saegersven/robocup24/tests/test.png

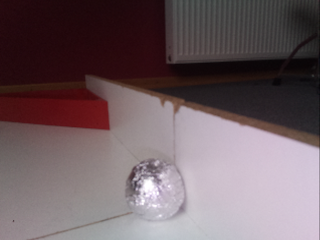
tests/test.png
