saegersven/robocup24/tests/tflite_c_api_test/test_images/1.png

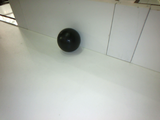
tests/tflite_c_api_test/test_images/1.png
