saegersven/robocup24/tests/tflite_c_api_test/test_images/3.png

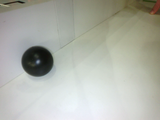
tests/tflite_c_api_test/test_images/3.png
