saegersven/robocup24/src/motions.h

/**************************************************************************************************************
 *                                                                                                            *
 * MOTIONS                                                                                                    *
 *                                                                                                            *
 * Contains specific movement sequences the robot does (e.g. picking up victims).                             *
 * This is all in a separate file to avoid cluttering the main program.                                       *
 *                                                                                                            *
 **************************************************************************************************************/

#pragma once

void pick_up_victim();
