saegersven/robocup24/src/rescue/rescue.c

#include "rescue.h"

#include <stdio.h>
#include <math.h>
#include <string.h>
#include <stdbool.h>

#include "../vision.h"
#include "../camera.h"
#include "../thresholding.h"
#include "../utils.h"
#include "../robot.h"

#include "victims.h"
#include "corner.h"
#include "silver.h"

// TuhDu (@Sven):
// cooldown when exit front detect
// test front exit

static DECLARE_S_IMAGE(frame, RESCUE_FRAME_WIDTH, RESCUE_FRAME_HEIGHT, 3);

// accurate flag uses rescue_reposition for improved accuracy
void rescue_find_center(bool accurate) {
	robot_serial_reset();
	const int MAX_TIME = 2500;

	for(int i = 0; i < 2; i++) {
		long long start_time = milliseconds();

		while(milliseconds() - start_time < MAX_TIME) {
			int dist = robot_sensor(DIST_FRONT);
			delay(30);
			if(dist > 800 && dist < 1100) {
				if(i == 1) {
					robot_drive(127, 35, 0);
				} else {
					robot_drive(35, 127, 0);
				}
			} else if (dist < 500) {
				if(i == 1) {
					robot_drive(-35, -127, 0);
				} else {
					robot_drive(-127, -35, 0);
				}
			} else {
				if(i == 1) {
					robot_drive(60, -60, 0);
				} else {
					robot_drive(-60, 60, 0);
				}
			}
		}
	}
	robot_drive(-80, -80, 300);
	robot_stop();

	if (accurate) rescue_reposition();
}

void rescue_reposition() {
	int dist_front = robot_distance_avg(DIST_FRONT, 10, 3);
	int dist_right_front = robot_distance_avg(DIST_RIGHT_FRONT, 10, 3);
	int dist_right_rear = robot_distance_avg(DIST_RIGHT_REAR, 10, 3);

	// exit somewhere, turn a bit and try again
	if ((dist_front > 1000) | (dist_right_front > 1000) | (dist_right_rear > 1000)) {
		robot_drive(100, -100, 73);
		rescue_reposition();
		return;
	}

	float x = (dist_right_front + dist_right_rear) / 2.0f - 500;
	float y = dist_front - 500;

	float angle = atan2f(x, y);
	float mag = sqrtf(x*x + y*y);

	robot_turn(angle);
	robot_drive(100, 100, mag * 2);
}

void rescue_collect_victim() {
	// DO THE COLLECTING THING
	robot_servo(SERVO_STRING, STRING_POS_OPEN, false, false);
    robot_servo(SERVO_ARM, ARM_POS_HALF_DOWN, false, false);
    delay(800);
    printf("Driving forward\n");
    robot_drive(70, 70, 0);
    delay(200);
    robot_servo(SERVO_ARM, ARM_POS_DOWN, true, true);
    delay(100);
    robot_stop();
    delay(300);
    robot_servo(SERVO_ARM, ARM_POS_DOWN, true, true);
    robot_drive(-70, -70, 200);
    robot_drive(70, 70, 200);
    delay(200);
    robot_servo(SERVO_STRING, STRING_POS_CLOSED, false, false);
    delay(450);
    robot_drive(-70, -70, 600);
    robot_servo(SERVO_ARM, ARM_POS_UP, false, false);
    delay(400);
}

// Returns 0 if no victim was found, 1 if victim is alive and 2 if victim is dead
int rescue_collect(int find_dead) {
	display_set_number(NUMBER_RESCUE_OBJECTIVE, RESCUE_OBJECTIVE_VICTIM);

	struct Victim victim;

	int cam_angle = CAM_POS_UP;
	robot_servo(SERVO_CAM, cam_angle, false, false);

	int final_approach = 0;

	int turn_counter = 0;
	int none_found_counter = 0;

	float classification_accumulator = 0.0f;
	int num_classifications = 0;
	//camera_start_capture(RESCUE_CAPTURE_WIDTH, RESCUE_CAPTURE_HEIGHT);
	while(1) {
		robot_stop();
		delay(60);
		camera_start_capture(RESCUE_CAPTURE_WIDTH, RESCUE_CAPTURE_HEIGHT);
		camera_grab_frame(frame, RESCUE_FRAME_WIDTH, RESCUE_FRAME_HEIGHT);
		camera_stop_capture();
		printf("Frame grabbed\n");
		int ret = victims_find(frame, find_dead, &victim);
		printf("%d\n", ret);
		delay(10);

		if(ret) {
			num_classifications++;
			classification_accumulator += victim.dead;
			display_set_number(NUMBER_RESCUE_POS_X, victim.x);
			display_set_number(NUMBER_RESCUE_POS_Y, victim.y);
			display_set_number(NUMBER_RESCUE_IS_DEAD, victim.dead + 1);

			float angle_horizontal = (victim.x - 0.5f) * CAM_HORIZONTAL_FOV;
			robot_turn(angle_horizontal);

			printf("Victim at (%f, %f)\n", victim.x, victim.y);

			if(final_approach) {
				int duration = (0.5f - victim.y) * 500;
				robot_drive(50, 50, duration);

				if(victim.x > 0.45f && victim.x < 0.55f
					&& victim.y > 0.42f && victim.y < 0.58f) {
					robot_turn(DTOR(30.0f));
					delay(50);
					robot_drive(-60, -60, 180);
					delay(50);
					rescue_collect_victim();
					//camera_stop_capture();
					return (int)roundf(classification_accumulator / num_classifications) + 1;
				}
			} else {
				float angle_vertical = (victim.y - 0.5f) * CAM_VERTICAL_FOV;
				printf("Angle vertical: %f\n", RTOD(angle_vertical));

				float alpha = DTOR(cam_angle - CAM_POS_HORIZONTAL) + angle_vertical;
				if(alpha < 0.1f) alpha = 0.1f;
				float dist = CAM_HEIGHT_MM / alpha;
				int duration = dist * 0.6f;
				printf("Duration: %d\n", duration);
				robot_drive(80, 80, duration);


				float beta = atanf(CAM_HEIGHT_MM / dist);
				if(dist < 400.0f) beta = 0.0f;
				printf("Beta: %f\n", beta);
				cam_angle += RTOD(angle_vertical + beta);

				printf("New cam angle: %d\n", cam_angle);

				robot_servo(SERVO_CAM, cam_angle, false, false);

				if(cam_angle > 110 && dist < 105.0f) {
					printf("Final approach\n");
					cam_angle = 120;
					robot_servo(SERVO_CAM, cam_angle, false, false);
					final_approach = 1;
				}
			}
		} else {
			display_set_number(NUMBER_RESCUE_POS_X, 0.0f);
			display_set_number(NUMBER_RESCUE_POS_Y, 0.0f);
			display_set_number(NUMBER_RESCUE_IS_DEAD, 0.0f);

			num_classifications = 0;
			classification_accumulator = 0.0f;

			cam_angle = CAM_POS_UP;
			robot_servo(SERVO_CAM, cam_angle, false, false);
			final_approach = 0;

			robot_turn(DTOR(30.0f));
			turn_counter++;
			delay(250);
			if(turn_counter == 12) {
				if(none_found_counter == 1) {
					find_dead = 1;
				}
				rescue_find_center(0);
				none_found_counter++;
				turn_counter = 0;
			}
		}
	}
}

int rescue_collect_test(int find_dead) {
	display_set_number(NUMBER_RESCUE_OBJECTIVE, RESCUE_OBJECTIVE_VICTIM);

	struct Victim victim;

	int cam_angle = CAM_POS_UP;
	robot_servo(SERVO_CAM, cam_angle, false, false);

	camera_start_capture(RESCUE_CAPTURE_WIDTH, RESCUE_CAPTURE_HEIGHT);

	while(1) {
		camera_grab_frame(frame, RESCUE_FRAME_WIDTH, RESCUE_FRAME_HEIGHT);

		int ret = victims_find(frame, find_dead, &victim);
		
		if(ret) {
			display_set_number(NUMBER_RESCUE_POS_X, victim.x);
			display_set_number(NUMBER_RESCUE_POS_Y, victim.y);
			display_set_number(NUMBER_RESCUE_IS_DEAD, victim.dead + 1);

			float angle_horizontal = (victim.x - 0.5f) * CAM_HORIZONTAL_FOV;
			
			float u = 20 * angle_horizontal;
			robot_drive(30 + u, 30 - u, 0);

			float angle_vertical = (victim.y - 0.5f) * CAM_VERTICAL_FOV;
			float v = 10 * angle_vertical;
			cam_angle += v;
			robot_servo(SERVO_CAM, cam_angle, false, false);
		} else {
			display_set_number(NUMBER_RESCUE_POS_X, 0.0f);
			display_set_number(NUMBER_RESCUE_POS_Y, 0.0f);
			display_set_number(NUMBER_RESCUE_IS_DEAD, 0.0f);

			cam_angle = CAM_POS_UP;
			robot_servo(SERVO_CAM, cam_angle, false, false);

			robot_turn(DTOR(30.0f));
			delay(250);
		}
	}
}

void rescue_drop_victim() {
	delay(200);
    robot_servo(SERVO_STRING, STRING_POS_OPEN, true, true);
    delay(500);
    robot_servo(SERVO_STRING, STRING_POS_OPEN, false, false);
    robot_servo(SERVO_ARM, ARM_POS_HALF_DOWN, true, true);
    delay(1000);
    robot_servo(SERVO_STRING, STRING_POS_CLOSED, true, true);
    delay(400);
    robot_servo(SERVO_STRING, STRING_POS_OPEN, false, false);
    delay(400);
    robot_servo(SERVO_ARM, ARM_POS_UP, true, true);
    delay(250);
    robot_servo(SERVO_ARM, ARM_POS_HALF_DOWN, true, true);
    delay(250);
    robot_servo(SERVO_ARM, ARM_POS_UP, true, true);
    delay(250);
    robot_servo(SERVO_ARM, ARM_POS_HALF_DOWN, true, true);
    delay(250);
    robot_servo(SERVO_ARM, ARM_POS_UP, false, false);
    delay(600);
}

void rescue_deliver(int is_dead) {
	display_set_number(NUMBER_RESCUE_OBJECTIVE, RESCUE_OBJECTIVE_CORNER);

	robot_servo(SERVO_CAM, CAM_POS_UP, false, false);
	
	delay(300);
	camera_start_capture(RESCUE_CAPTURE_WIDTH, RESCUE_CAPTURE_HEIGHT);
	for(int i = 0; i < 5; i++) camera_grab_frame(frame, RESCUE_FRAME_WIDTH, RESCUE_FRAME_HEIGHT);
	camera_stop_capture();
	delay(200);
	//camera_start_capture(RESCUE_CAPTURE_WIDTH, RESCUE_CAPTURE_HEIGHT);

	long long start_time = milliseconds();

	int turn_counter = 0;
	while(1) {
		robot_turn(DTOR(20.0f));
		delay(250);

		camera_start_capture(RESCUE_CAPTURE_WIDTH, RESCUE_CAPTURE_HEIGHT);
		camera_grab_frame(frame, RESCUE_FRAME_WIDTH, RESCUE_FRAME_HEIGHT);
		camera_stop_capture();

		delay(50);

		float x = 0.0f;
		if(corner_detect(frame, &x, !is_dead, milliseconds() - start_time)) {
			printf("Corner pos: %f\n", x);

			robot_stop();
			delay(50);

			robot_turn(x * DTOR(65.0f) + DTOR(1.0f));

			int alignment_successful = 1;
			// Align for final approach
			for(int i = 0; i < 8; i++) {
				camera_start_capture(RESCUE_CAPTURE_WIDTH, RESCUE_CAPTURE_HEIGHT);
				camera_grab_frame(frame, RESCUE_FRAME_WIDTH, RESCUE_FRAME_HEIGHT);
				camera_stop_capture();
				delay(50);

				if(!corner_detect(frame, &x, !is_dead, milliseconds() - start_time)) {
					if(i < 3) {
						printf("Lost corner");
						robot_turn(-DTOR(20.0f));
						alignment_successful = 0;
					}
					x = 0.0f;
					break;
				}

				robot_turn(x * DTOR(65.0f) + DTOR(1.0f));
				if(i > 1) robot_drive(45, 45, 700);
				delay(80);
			}

			if(!alignment_successful) continue;

			// Robot is aligned with corner, approach

			/*
			robot_drive(40, 40, 1600);
			robot_drive(-80, -80, 200);
			robot_turn(DTOR(25.0f));
			robot_drive(40, 40, 650);
			*/
			robot_drive(-100, 0, 250);
			robot_drive(0, -100, 350);
			robot_drive(40, 40, 1150);

			// Drop victim
			rescue_drop_victim();

			// Go back to center
			if (!is_dead) {
				robot_drive(-100, -100, 600);
				robot_turn(DTOR(45.0f)); // face away from corner to avoid detecting rescued victims (just to be safe)
			}

			//camera_stop_capture();
			return;
		}

		turn_counter++;

		if(turn_counter == 18) {
			rescue_find_center(0);

			turn_counter = 0;
		}
	}
}

const int CAPTURE_WIDTH = 320;
const int CAPTURE_HEIGHT = 192;
const int FRAME_WIDTH = 80;
const int FRAME_HEIGHT = 48;

// Counts red/green pixels
bool rescue_is_corner() {
	robot_servo(SERVO_CAM, 0.4 * (CAM_POS_UP + CAM_POS_DOWN), true, false);
	delay(300);

	const int NUM_PIXELS_THRESHOLD = 360;

	camera_grab_frame(frame, FRAME_WIDTH, FRAME_HEIGHT);

	int green_pixels = image_count_pixels(frame, FRAME_WIDTH, FRAME_HEIGHT, 3, is_green);
	int red_pixels = image_count_pixels(frame, FRAME_WIDTH, FRAME_HEIGHT, 3, is_red);

	printf("Num green pixels: %d \t Red pixels: %d \n", green_pixels, red_pixels);

	return green_pixels > NUM_PIXELS_THRESHOLD || red_pixels > NUM_PIXELS_THRESHOLD;
}

int is_black_exit(uint8_t b, uint8_t g, uint8_t r) {
	return (uint16_t)b + (uint16_t)g + (uint16_t)r < 120;
}

int is_gray(uint8_t b, uint8_t g, uint8_t r) {
	return (uint16_t)b + (uint16_t)g + (uint16_t)r < 250;
}

// Lets hope num black pixels is enough
bool rescue_is_exit() {
	//return true;
	const int NUM_PIXELS_THRESHOLD = 340;
	
	int max_num_pixels = 0;

	robot_drive(60, 60, 0);
	long long start_time = milliseconds();

	int sum_black_pixels = 0;
	const int N = 5;

	for(int i = 0; i < N; i++) {
		camera_grab_frame(frame, FRAME_WIDTH, FRAME_HEIGHT);

		int num_black_pixels = image_count_pixels_roi(frame, FRAME_WIDTH, FRAME_HEIGHT, 3, is_black_exit, 20, 60, 5, 43);
		sum_black_pixels += num_black_pixels;
		printf("Num black pixels: %d\n", num_black_pixels);

		if(num_black_pixels > max_num_pixels) max_num_pixels = num_black_pixels;

		robot_drive(60, 60, 80);
	}

	int avg_black_pixels = sum_black_pixels / N;

	printf("avg_black_pixels: %d\n", avg_black_pixels);
	printf("max_num_pixels: %d\n", max_num_pixels);

	return max_num_pixels > NUM_PIXELS_THRESHOLD;
}

// returns number of black pixels in current frame
int pixels_black() {
	robot_servo(SERVO_CAM, CAM_POS_DOWN - 10, true, false);
	delay(300);

	camera_start_capture(RESCUE_CAPTURE_WIDTH, RESCUE_CAPTURE_HEIGHT);
	camera_grab_frame(frame, RESCUE_FRAME_WIDTH, RESCUE_FRAME_HEIGHT);
	camera_stop_capture();
	printf("Black pixels: %d \n", image_count_pixels(frame, RESCUE_FRAME_WIDTH, RESCUE_FRAME_HEIGHT, 3, is_black));
    return image_count_pixels(frame, RESCUE_FRAME_WIDTH, RESCUE_FRAME_HEIGHT, 3, is_black);
}

// navigates around corner
int rescue_navigate_corner() {
	if (robot_distance_avg(DIST_RIGHT_FRONT, 10, 0.2f) < 70) {
		robot_drive(0, -100, 300);
		robot_drive(-100, 0, 400);
		robot_drive(40, 40, 1100);
	}
	robot_drive(-100, -100, 300);
	robot_turn(-R90);
	if (robot_distance_avg(DIST_FRONT, 10, 0.2f) > 1500) { //ohohoho exit in front
		
		camera_start_capture(RESCUE_CAPTURE_WIDTH, RESCUE_CAPTURE_HEIGHT);
		while(1) {
			robot_drive(60, 60, 0);
			camera_grab_frame(frame, RESCUE_FRAME_WIDTH, RESCUE_FRAME_HEIGHT);
			int num_pixels = image_count_pixels(frame, RESCUE_FRAME_WIDTH, RESCUE_FRAME_HEIGHT, 3, is_black);
			if(num_pixels > 200) break;
		}
		camera_stop_capture();

		robot_turn(DTOR(45.0f));
		robot_drive(100, 100, 300);

		return 1;
	} else {
		robot_drive(50, 50, 0);
		while (robot_sensor(DIST_FRONT) > 200);
		robot_stop();
		robot_turn(DTOR(135.0f));
		robot_drive(-100, -100, 250);
		robot_turn(-DTOR(175.0f));
		robot_drive(-100, -100, 250);
	}
	return 0;
}

void rescue_find_exit() {
	printf("I am in find exit now. Pls pray for me.\n");
	if(rescue_navigate_corner()) return;

	bool already_checked_for_corner = false;
	long long side_exit_cooldown = 0;

	long long last_time = milliseconds();
	int prev_error = 0;

	robot_servo(SERVO_CAM, CAM_POS_DOWN - 5, true, false);

	rescue_silver_init();

	camera_start_capture(CAPTURE_WIDTH, CAPTURE_HEIGHT);

	while(1) {
		int front_dist = robot_sensor(DIST_FRONT);
		int side_front_dist = robot_sensor(DIST_RIGHT_FRONT);
		int side_rear_dist = robot_sensor(DIST_RIGHT_REAR);

		// --- START OF WALLFOLLOWER LOGIC ---
		if(side_front_dist < 200 && side_rear_dist < 200) {
			const int SPEED = 50;
			const int TARGET_DIST_SIDE = 50;   // Target distance for the side sensor
			
			const float L = 113.0f;
			const float delta_D = 8.0f;

			const float KP = 0.4f;
			const float KD = 0.02f;
			const float KP_angle = 80.0f;

			float angle = atanf((float)(side_rear_dist + delta_D - side_front_dist) / L);

			// PD controller for side distance
			int side_dist_measurement = TARGET_DIST_SIDE - (side_front_dist + side_rear_dist + delta_D) / 2;
			float error = side_dist_measurement * cosf(angle);

			printf("Error: %.0f, Angle: %.2f\n", error, angle);

			long long time = milliseconds();
			float dt = (time - last_time) / 1000.0f;
			if(prev_error == 0) prev_error = error;
			float derivative = (error - prev_error) / dt;
			last_time = time;
			prev_error = error;

			int speed_adjustment = clamp(KP * error + KD * derivative + KP_angle * angle, -50, 50);

			int left_speed = SPEED - speed_adjustment;
			int right_speed = SPEED + speed_adjustment;

			// Only drive with calculates speeds when there is a wall
			robot_drive(left_speed, right_speed, 0);
		} else {
			robot_drive(50, 50, 0);
		}
		// --- END OF WALLFOLLOWER LOGIC ---

		// Check for exit with camera
		camera_grab_frame(frame, FRAME_WIDTH, FRAME_HEIGHT);

		int num_black_pixels = image_count_pixels(frame, FRAME_WIDTH, FRAME_HEIGHT, 3, is_gray);
		if(num_black_pixels > 400) {
			printf("Potential front exit\n");

			robot_stop();
			if(rescue_silver_detect_flipped(frame, 3) > 0.5f) {
				robot_drive(-60, -60, 150);
				if (!rescue_is_exit()) {
					// no exit, skip
					robot_drive(-80, -80, 500);
					robot_turn(DTOR(90.0f));
					robot_drive(-100, -100, 400);
					robot_turn(DTOR(-180.0f));
					robot_drive(-50, -50, 1200);
					side_exit_cooldown = milliseconds();
				} else return;
			}
		}

		// There are 4 different cases:

		// 1) 35cm in front of wall, check for corner
		// 2) 10cm in front of wall, turn 90°
		// 3) potential exit front
		// 4) potential exit side

		// 1. case
		if (!already_checked_for_corner &&
			front_dist < 360
			&& robot_stop()
			&& robot_distance_avg(DIST_FRONT, 5, 1) < 380) {

			printf("Case 1\n");
			if (rescue_is_corner()) {
				robot_drive(-100, -100, 200);
				delay(30);
				robot_turn(DTOR(132.0f));
				robot_drive(-100, -100, 300);
				robot_turn(-R90);
				robot_drive(40, 40, 1500);
				if(rescue_navigate_corner()) return;
			} else {
				already_checked_for_corner = true;
			}

			robot_servo(SERVO_CAM, CAM_POS_DOWN - 5, true, false);
		}

		// 2. case
		else if (front_dist < 130
			&& robot_stop()
			&& robot_distance_avg(DIST_FRONT, 5, 1) < 150) {

			printf("Case 2\n");
			robot_turn(DTOR(90.0f));
			robot_drive(-100, -100, 250);
			robot_turn(DTOR(-180.0f));
			robot_drive(-50, -50, 400);
			if (already_checked_for_corner) {
				robot_drive(-50, -50, 800);
			}
			already_checked_for_corner = false;
		}

		// 4. case
		if (milliseconds() - side_exit_cooldown > 3000 
			&& side_front_dist > 200 
			&& robot_stop() 
			&& robot_distance_avg(DIST_RIGHT_FRONT, 5, 1) > 180) {

			printf("Potential side exit\n");
			robot_drive(100, 100, 180);
			robot_turn(DTOR(90.0f));

			if (!rescue_is_exit()) {
				// no exit, skip
				robot_drive(-80, -80, 400);
				robot_turn(DTOR(-90.0f));
				side_exit_cooldown = milliseconds();
			} else {
				robot_drive(100, 100, 150);
				return;
			}
		}
	}
}
void rescue() {
	display_set_mode(MODE_RESCUE);
	display_set_image(IMAGE_RESCUE_FRAME, frame);
	display_set_image(IMAGE_RESCUE_THRESHOLD, corner_thresh);

	robot_serial_reset();

	robot_drive(100, 100, 800);

	int dist = robot_distance_avg(DIST_RIGHT_FRONT, 10, 2);
	printf("Dist right front: %d\n", dist);
	if(dist < 400) {
		robot_turn(DTOR(130.0f));
		robot_drive(-100, -100, 800);
		robot_turn(DTOR(85.0f));
	} else {
		robot_turn(DTOR(-130.0f));
		robot_drive(-100, -100, 800);
		robot_turn(DTOR(120.0f));
	}

	//camera_start_capture(RESCUE_CAPTURE_WIDTH, RESCUE_CAPTURE_HEIGHT);


	robot_servo(SERVO_CAM, CAM_POS_UP, false, false);
	robot_servo(SERVO_ARM, ARM_POS_UP, false, false);
	robot_servo(SERVO_STRING, STRING_POS_OPEN, false, false);

	victims_init();
	corner_init();

	display_set_number(NUMBER_RESCUE_OBJECTIVE, RESCUE_OBJECTIVE_VICTIM);

	int num_victims = 0;

	while(num_victims < 3) {
		display_set_number(NUMBER_RESCUE_NUM_VICTIMS, num_victims);

		int ret = rescue_collect(num_victims >= 2);

		if(ret) {
			rescue_deliver(ret == 2);
			if(ret == 2) {
				break;
			}
		} else {
			rescue_find_center(0);
			robot_drive(-70, -70, 400);
		}
		
		num_victims++;
	}
	robot_drive(35, 35, 1000);
	rescue_find_exit();

	rescue_cleanup();
}

void rescue_cleanup() {
	victims_destroy();
	corner_destroy();
	camera_stop_capture();
	delay(100);
}
