saegersven/robocup24/src/camera.c

#include "camera.h"

#include <string.h>
#include <stdio.h>
#include <stdint.h>
#include <errno.h>
#include <fcntl.h>
#include <sys/ioctl.h>
#include <sys/types.h>
#include <sys/time.h>
#include <sys/mman.h>
#include <linux/videodev2.h>
#include <pthread.h>
#include "../libs/libv4l/include/libv4l2.h"

#include "utils.h"

// Safe ioctl
static void xioctl(int fh, int request, void *arg) {
    int r;
    do {
        r = v4l2_ioctl(fh, request, arg);
    } while(r == -1 && ((errno = EINTR) || (errno == EAGAIN)));

    if(r == -1) {
	    fprintf(stderr, "error %d, %s\n", errno, strerror(errno));
	    exit(EXIT_FAILURE);
    }
}

static pthread_mutex_t frame_lock = PTHREAD_MUTEX_INITIALIZER;
static uint8_t *current_frame_ptr;
uint32_t current_width, current_height;
static uint32_t requested_width, requested_height;
static int has_frame;

static pthread_mutex_t signal_lock = PTHREAD_MUTEX_INITIALIZER;
static int stop_signal;

static pthread_t capture_thread_id;

static int camera_fd;

static const int NUM_BUFFERS = 2;

static int camera_running = 0;

void camera_start_capture(int width, int height) {
    stop_signal = 0;
    has_frame = 0;

    struct image_size *size = malloc(sizeof(struct image_size));
    size->width = width;
    size->height = height;
    requested_width = width;
    requested_height = height;
    
    pthread_create(&capture_thread_id, NULL, camera_capture_loop, (void*)size);
    pthread_detach(capture_thread_id);

    camera_running = 1;
}

void camera_stop_capture() {
    if(!camera_running) return;
    camera_running = 0;

    pthread_mutex_lock(&signal_lock);
    stop_signal = 1;
    pthread_mutex_unlock(&signal_lock);
}

void camera_grab_frame(uint8_t *frame, uint32_t width, uint32_t height) {
    pthread_mutex_lock(&frame_lock);

    // TODO: Add timeout
    while(!has_frame) {
        pthread_mutex_unlock(&frame_lock);
        usleep(100);
        pthread_mutex_lock(&frame_lock);
    }
    float factor_x = (float)requested_width / width;
    float factor_y = (float)requested_height / height;

    for(int i = 0; i < height; i++) {
        for(int j = 0; j < width; j++) {

            int dest_idx = i * width + j;
            int src_idx = factor_y * (height - 1 - i) * requested_width + factor_x * (width - 1 - j);

            for(int k = 0; k < 3; k++) {
                frame[3*dest_idx + k] = current_frame_ptr[3*src_idx + k];
            }
        }
    }

    has_frame = 0;

    pthread_mutex_unlock(&frame_lock);
}

void *camera_capture_loop(void *size) {
    pthread_detach(pthread_self());

    struct v4l2_format          fmt;
    struct v4l2_buffer          buf;
    struct v4l2_requestbuffers  req;
    enum v4l2_buf_type          type;
    fd_set                      fds;
    struct timeval              tv;
    int                         r, fd = -1;
    unsigned int                i, n_buffers;
    char                        *dev_name = "/dev/video0";
    struct image_data_buffer    *buffers;

    unsigned int width = ((struct image_size*)size)->width;
    unsigned int height = ((struct image_size*)size)->height;

    fd = v4l2_open(dev_name, O_RDWR | O_NONBLOCK, 0);
    if(fd < 0) {
        fprintf(stderr, "Could not open camera device\n");
        exit(EXIT_FAILURE);
    }

    CLEAR(fmt);
    fmt.type = V4L2_BUF_TYPE_VIDEO_CAPTURE;
    fmt.fmt.pix.width       = width;
    fmt.fmt.pix.height      = height;
    fmt.fmt.pix.pixelformat = V4L2_PIX_FMT_BGR24;
    fmt.fmt.pix.field       = V4L2_FIELD_INTERLACED;
    xioctl(fd, VIDIOC_S_FMT, &fmt);

    if(fmt.fmt.pix.pixelformat != V4L2_PIX_FMT_BGR24) {
        printf("Libv4l did not accept BGR24 format\n");
        exit(EXIT_FAILURE);
    }

    if(fmt.fmt.pix.width != width || (fmt.fmt.pix.height != height)) {
        printf("Driver is sending image at %dx%d\n",
            fmt.fmt.pix.width, fmt.fmt.pix.height);
    }

    CLEAR(req);
    req.count = 2;
    req.type = V4L2_BUF_TYPE_VIDEO_CAPTURE;
    req.memory = V4L2_MEMORY_MMAP;
    xioctl(fd, VIDIOC_REQBUFS, &req);

    buffers = calloc(req.count, sizeof(*buffers));
    for(n_buffers = 0; n_buffers < req.count; ++n_buffers) {
        CLEAR(buf);

        buf.type    = V4L2_BUF_TYPE_VIDEO_CAPTURE;
        buf.memory  = V4L2_MEMORY_MMAP;
        buf.index   = n_buffers;

        xioctl(fd, VIDIOC_QUERYBUF, &buf);

        buffers[n_buffers].length = buf.length;
        buffers[n_buffers].start = v4l2_mmap(NULL, buf.length,
            PROT_READ | PROT_WRITE, MAP_SHARED, fd, buf.m.offset);

        if(MAP_FAILED == buffers[n_buffers].start) {
            fprintf(stderr, "mmap failed\n");
            exit(EXIT_FAILURE);
        }
    }

    for(i = 0; i < n_buffers; ++i) {
        CLEAR(buf);
        buf.type    = V4L2_BUF_TYPE_VIDEO_CAPTURE;
        buf.memory  = V4L2_MEMORY_MMAP;
        buf.index = i;
        xioctl(fd, VIDIOC_QBUF, &buf);
    }
    type = V4L2_BUF_TYPE_VIDEO_CAPTURE;

    xioctl(fd, VIDIOC_STREAMON, &type);
    while(1) {
        do {
            FD_ZERO(&fds);
            FD_SET(fd, &fds);

            /* Timeout */
            tv.tv_sec = 2;
            tv.tv_usec = 0;

            r = select(fd + 1, &fds, NULL, NULL, &tv);
        } while((r == -1) && (errno == EINTR));

        if(r == -1) {
            fprintf(stderr, "select failed\n");
            exit(EXIT_FAILURE);
        }

        CLEAR(buf);
        buf.type = V4L2_BUF_TYPE_VIDEO_CAPTURE;
        buf.memory = V4L2_MEMORY_MMAP;
        xioctl(fd, VIDIOC_DQBUF, &buf);

        /* Convert to image */
        pthread_mutex_lock(&frame_lock);
        current_width = fmt.fmt.pix.width;
        current_height = fmt.fmt.pix.height;
        current_frame_ptr = buffers[buf.index].start;

        has_frame = 1;
        pthread_mutex_unlock(&frame_lock);

        /* Check if stop signal was activated */
        pthread_mutex_lock(&signal_lock);
        int sig = stop_signal;
        pthread_mutex_unlock(&signal_lock);
        if(sig) {
            type = V4L2_BUF_TYPE_VIDEO_CAPTURE;
            xioctl(fd, VIDIOC_STREAMOFF, &type);
            for(i = 0; i < n_buffers; ++i) {
                v4l2_munmap(buffers[i].start, buffers[i].length);
            }
            v4l2_close(fd);
            
            pthread_exit(NULL);
        }

        /* Queue next buffer */
        xioctl(fd, VIDIOC_QBUF, &buf);

        usleep(70);
    }
}
