saegersven/robocup24/src/vision.c

#include "vision.h"

#include <stdio.h>

#define STB_IMAGE_WRITE_IMPLEMENTATION
#include "../libs/stb_image_write.h"

void copy_image(S_IMAGE(src), S_IMAGE(dest)) {
    if(src_w != dest_w || src_h != dest_h || src_c != dest_c) {
        fprintf(stderr, "copy_image: mismatched sizes");
        return;
    }

    memcpy(dest_d, src_d, src_w * src_h * src_c);
}

void read_raw_image(const char* path, uint8_t *img) {
    FILE* f = fopen(path, "r");

    uint32_t img_width, img_height;
    fread(&img_width, sizeof(uint32_t), 1, f);
    fread(&img_height, sizeof(uint32_t), 1, f);
    fread(img, sizeof(uint8_t), img_width * img_height * 3, f);

    fclose(f);
}

void write_image(const char* path, S_IMAGE(img)) {
    stbi_write_png(path, img_w, img_h, img_c, img_d, img_w * img_c);
}

void resize_image(S_IMAGE(src), S_IMAGE(dest), int new_width, int new_height) {
    if(dest_w != new_width || dest_h != new_height || src_c != dest_c) {
        fprintf(stderr, "resize_image: mismatched sizes");
        return;
    }

    for(int i = 0; i < new_height; i++) {
        for(int j = 0; j < new_width; j++) {
            int dest_idx = src_c * (i * new_width + j);
            int src_i = i * (float)src_h / new_height;
            int src_j = j * (float)src_w / new_width;
            int src_idx = src_c * (src_i * src_w + src_j);

            for(int k = 0; k < src_c; k++) {
                dest_d[dest_idx + k] = src_d[src_idx + k];
            }
        }
    }
}

void box_blur(S_IMAGE(src), uint8_t *dest, int kernel_size, int iterations) {
    uint8_t src_arr[src_w * src_h * src_c];
    memcpy(src_arr, src_d, sizeof(uint8_t) * src_w * src_h * src_c);
    
    memset(dest, 0, sizeof(uint8_t) * src_w * src_h * src_c);

    for(int it = 0; it < iterations; it++) {
        for(int i = 0; i < src_h; i++) {
            for(int j = 0; j < src_w; j++) {
                for(int k = 0; k < src_c; k++) {
                    int idx = src_c * (i * src_w + j) + k;

                    int kernel_size_y = kernel_size; 
                    if(i - kernel_size / 2 < 0) {
                        kernel_size_y += i - kernel_size / 2;
                    }
                    if(i + kernel_size / 2 > src_h - 1) {
                        kernel_size_y -= i + kernel_size / 2 - src_h + 1;
                    }
                    
                    int kernel_size_x = kernel_size;
                    if(j - kernel_size / 2 < 0) {
                        kernel_size_x += j - kernel_size / 2;
                    }
                    if(j + kernel_size / 2 > src_w - 1) {
                        kernel_size_x -= j + kernel_size / 2 - src_w + 1;
                    }
                    
                    int kernel_area = kernel_size_x * kernel_size_y;
                    
                    int accumulator = 0;
                    for(int x = -kernel_size / 2; x < kernel_size / 2 + 1; x++) {
                        int x_idx = j + x;
                        
                        if(x_idx < 0 || x_idx > src_w - 1) {
                            continue;
                        }
                        
                        for(int y = -kernel_size / 2; y < kernel_size / 2 + 1; y++) {
                            int y_idx = i + y;
                            
                            if(y_idx < 0 || x_idx > src_h - 1) {
                                continue;
                            }
                            
                            int k_idx = src_c * (y_idx * src_w + x_idx) + k;
                            accumulator += src_arr[k_idx];
                        }
                    }
                    
                    dest[idx] = accumulator / kernel_area;
                }
            }
        }
        
        if(it != iterations - 1) {
            memcpy(src_arr, dest, sizeof(uint8_t) * src_w * src_h * src_c);
        }
    }
}

float average_difference(uint8_t *one, S_IMAGE(two)) {
    float diff = 0.0f;
    for(int i = 0; i < two_w * two_h * two_c; i++) {
        diff += fabsf(one[i] - two_d[i]);
    }
    return diff / (two_w * two_h * two_c);
}
