saegersven/robocup24/src/utils.c

#include "utils.h"

#include <time.h>
#include <unistd.h>

long long milliseconds() {
    struct timeval tv;

    gettimeofday(&tv, NULL);
    return (((long long)tv.tv_sec)*1000 + tv.tv_usec/1000);
}

long long microseconds() {
    struct timeval tv;

    gettimeofday(&tv, NULL);
    return (((long long)tv.tv_sec)*1000000 + tv.tv_usec);
}

void delay(unsigned int milliseconds) {
    usleep(milliseconds * 1000);
}

int clamp(int value, int min, int max) {
    return value > min ? (value < max ? value : max) : min;
}

float clampf(float value, float min, float max) {
    return value > min ? (value < max ? value : max) : min;
}

int compare_float(const void *elem1, const void *elem2) {
    float f = *((float*)elem1);
    float s = *((float*)elem2);
    if(f > s) return 1;
    if(f < s) return -1;
    return 0;
}
