saegersven/robocup24/src/utils.h

/****************************************************************************************************************
 *                                                                                                              *
 * UTILS                                                                                                        *
 *                                                                                                              *
 * Provides utility functions for time and constants.                                                           *
 *                                                                                                              *
 * FOR_MILLIS(milliseconds)               - Loop that runs for a specified duration                             *
 * CLEAR(x)                               - Writes zeroes to memory of x                                        *
 *                                                                                                              *
 * millis()                               - Returns milliseconds since the UNIX epoch                           *
 * delay(milliseconds)                    - Wait for a specified duration                                       *
 *                                                                                                              *
 * float_comparison(elem1, elem2)         - Compares two floats                                                 *
 *                                                                                                              *
 ****************************************************************************************************************/

#pragma once

#include <stdlib.h>
#include <stdint.h>

// Constants
#define PI 3.141592653f
#define R180 PI
#define R90 (PI/2.0f)

// Macros
#define FOR_MILLIS_VAR(ms, var) long long var = millis(); \
    while(millis() - var < ms)

#define FOR_MILLIS(ms) FOR_MILLIS_VAR(ms, start_time)

#define CLEAR(x) memset(&(x), 0, sizeof(x))

#define DTOR(x) ((x)/180.0f*PI)
#define RTOD(x) ((x)*180.0f/PI)

// Time functions
long long milliseconds();
long long microseconds();
void delay(unsigned int milliseconds);

int clamp(int value, int min, int max);
float clampf(float value, float min, float max);

// Compares two floats (passed to qsort)
int float_comparison(const void *elem1, const void *elem2);
